moisesfa/lorawan-cuida-tu-planta/hardware/Adaptador_CubeCell_v1/docs/HTCC-AB01_V2.png

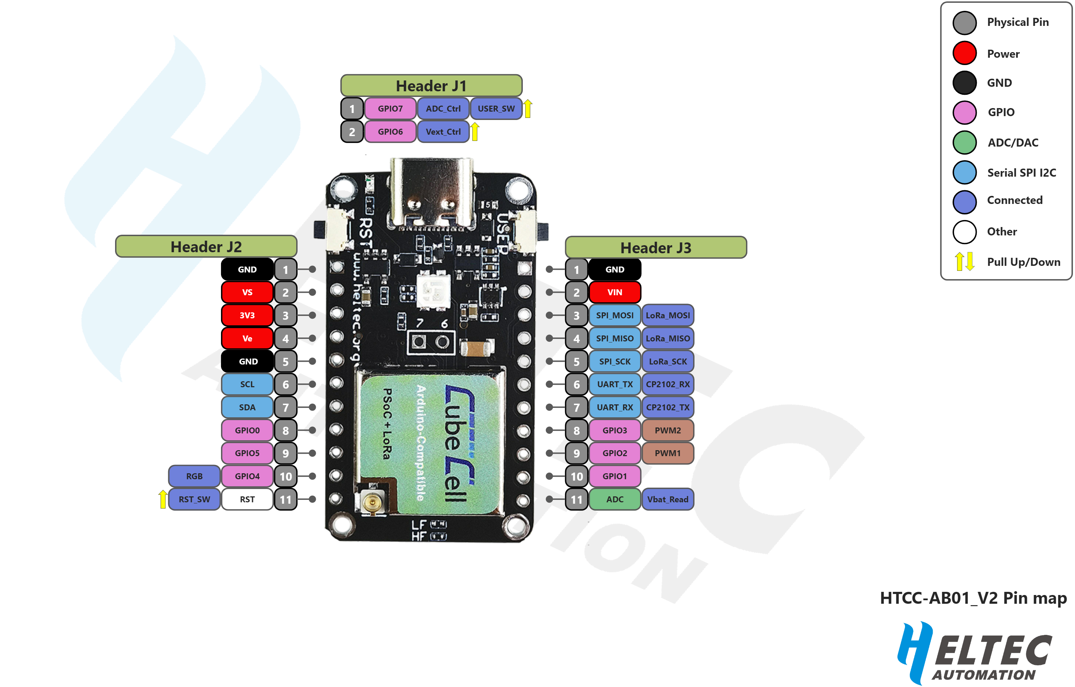
hardware/Adaptador_CubeCell_v1/docs/HTCC-AB01_V2.png
