moisesfa/lorawan-cuida-tu-planta/software/docs/Cuitupla.drawio0.png

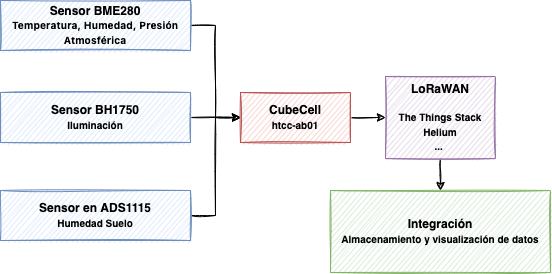
software/docs/Cuitupla.drawio0.png
