moisesfa/lorawan-cuida-tu-planta/software/02_inicio_bme280/src/main.cpp

#include <Arduino.h>

/*
 * bme280_example.ino
 * Example sketch for bme280
 *
 * Copyright (c) 2016 seeed technology inc.
 * Website    : www.seeedstudio.com
 * Author     : Lambor
 * Create Time:
 * Change Log :
 *
 * The MIT License (MIT)
 *
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
 * THE SOFTWARE IS PROVIDED "AS IS", WITHOUT WARRANTY OF ANY KIND, EXPRESS OR
 * IMPLIED, INCLUDING BUT NOT LIMITED TO THE WARRANTIES OF MERCHANTABILITY,
 * FITNESS FOR A PARTICULAR PURPOSE AND NONINFRINGEMENT. IN NO EVENT SHALL THE
 * AUTHORS OR COPYRIGHT HOLDERS BE LIABLE FOR ANY CLAIM, DAMAGES OR OTHER
 * LIABILITY, WHETHER IN AN ACTION OF CONTRACT, TORT OR OTHERWISE, ARISING FROM,
 * OUT OF OR IN CONNECTION WITH THE SOFTWARE OR THE USE OR OTHER DEALINGS IN
 * THE SOFTWARE.
 */
#include "CubeCell_NeoPixel.h"
CubeCell_NeoPixel pixels(1, RGB, NEO_GRB + NEO_KHZ800);
uint8_t i=0;


#include "Seeed_BME280.h"
#include <Wire.h>

BME280 bme280;

void setup()
{
  pinMode(Vext, OUTPUT);
  digitalWrite(Vext, LOW);
  
  pixels.begin(); // INITIALIZE NeoPixel strip object (REQUIRED)
  pixels.clear(); // Set all pixel colors to 'off'
  
  delay(500);

  Serial.begin(115200);
  if(!bme280.init()){
    Serial.println("Device error!");
  }
}

void loop()
{
  float pressure;

  //get and print temperatures
  Serial.print("Temp: ");
  Serial.print(bme280.getTemperature());
  Serial.println("C");//The unit for  Celsius because original arduino don't support speical symbols

  //get and print atmospheric pressure data
  Serial.print("Pressure: ");
  Serial.print(pressure = bme280.getPressure());
  Serial.println("Pa");

  //get and print altitude data
  Serial.print("Altitude: ");
  Serial.print(bme280.calcAltitude(pressure));
  Serial.println("m");

  //get and print humidity data
  Serial.print("Humidity: ");
  Serial.print(bme280.getHumidity());
  Serial.println("%");

  pixels.setPixelColor(0, pixels.Color(0, i, 0));
  pixels.show();   // Send the updated pixel colors to the hardware.
  
  delay(1000);
  i+=10;
  if (i>100) i =0;

}
